Abdenry/sensorHubProject/CAD/FreeCAD/weatherStation/components/conduit/box/20241117_102958.jpg

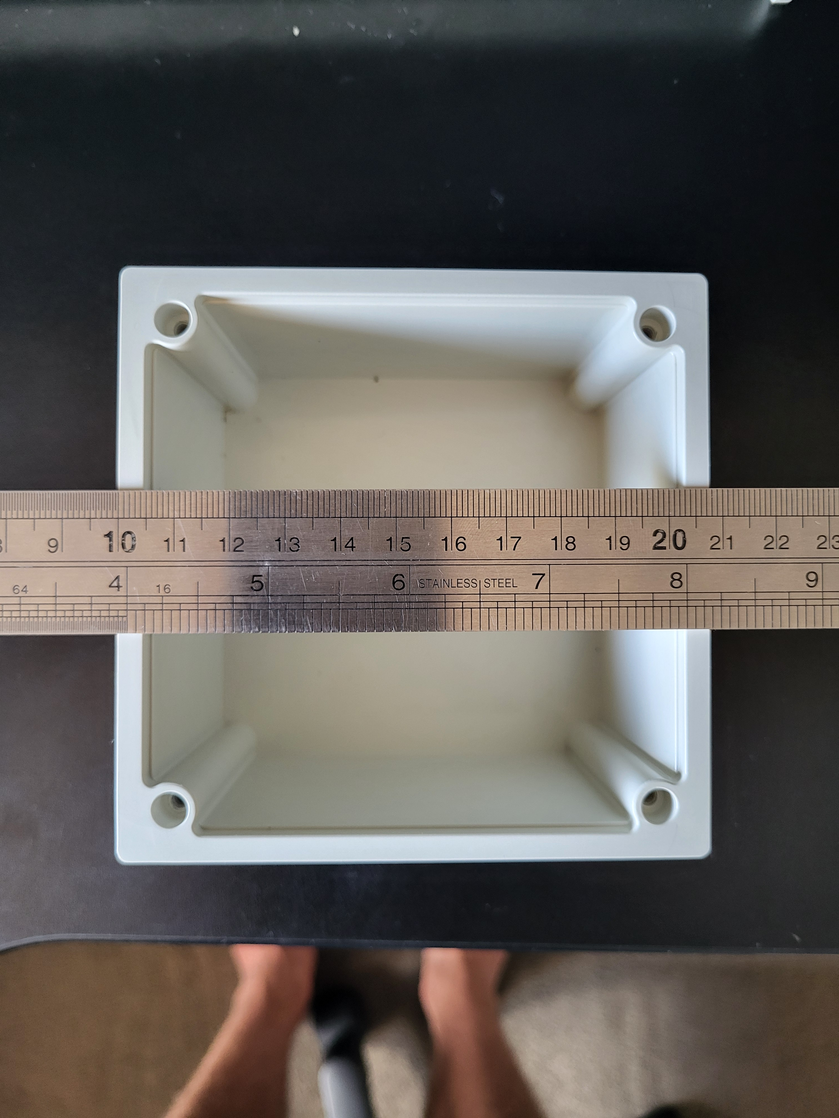
CAD/FreeCAD/weatherStation/components/conduit/box/20241117_102958.jpg
