Abdenry/sensorHubProject/CAD/FreeCAD/weatherStation/windVane/base/base.FCStd

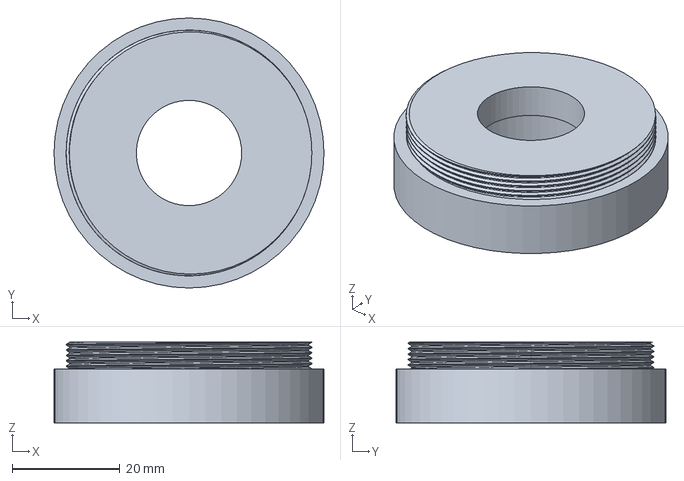
[picture p18: CAD file, 2025-01-13]
CAD/FreeCAD/weatherStation/windVane/base/base.FCStd
50.0 x 50.0 x 15.0 mm
