Abdenry/sensorHubProject/CAD/FreeCAD/weatherStation/windVane/middle/middle.FCStd

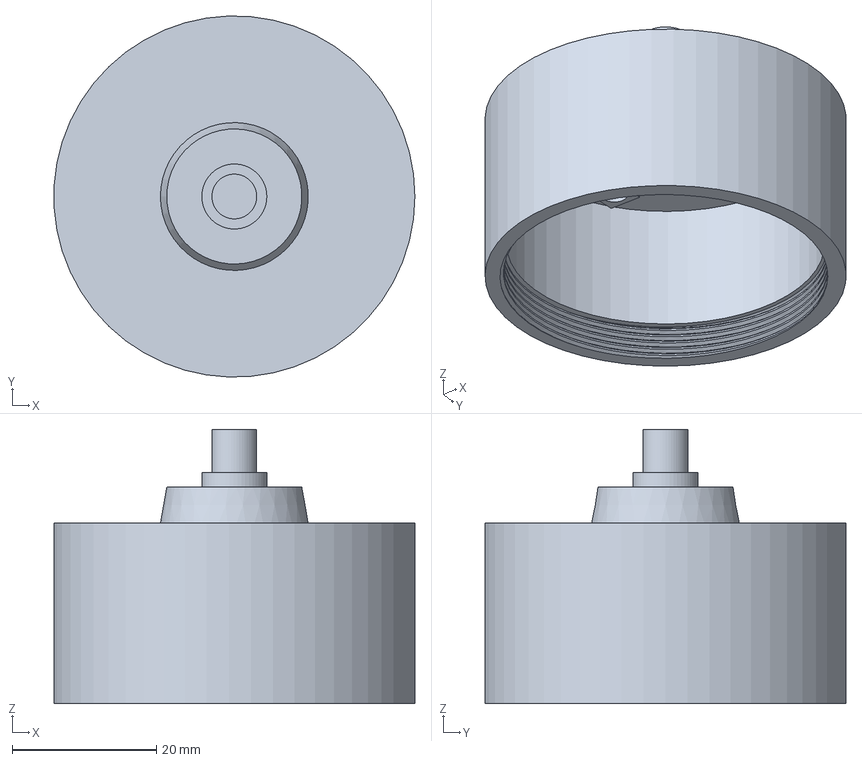
[picture p19: CAD file, 2025-01-13]
CAD/FreeCAD/weatherStation/windVane/middle/middle.FCStd
50.0 x 50.0 x 38.0 mm
