Abdenry/sensorHubProject/CAD/FreeCAD/weatherStation/windVane/top/top.FCStd

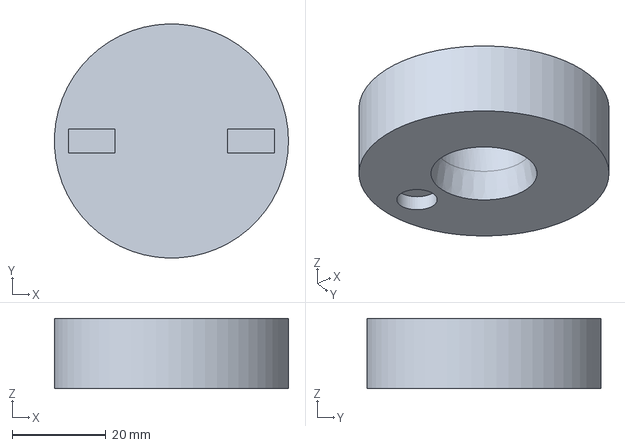
[picture p20: CAD file, 2025-03-11]
CAD/FreeCAD/weatherStation/windVane/top/top.FCStd
50.0 x 50.0 x 15.0 mm
