Abdenry/sensorHubProject/CAD/FreeCAD/weatherStation/windVane/vane/vane-Body.stl

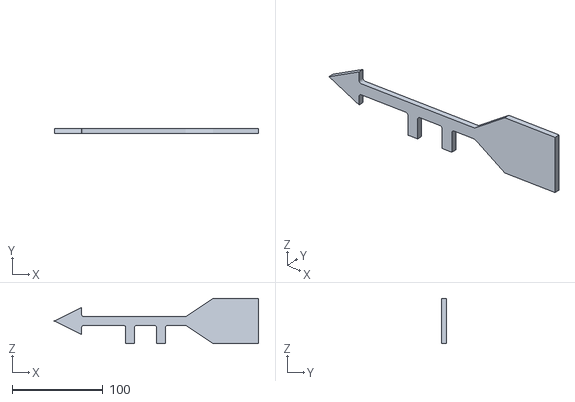
[picture p21: CAD file, 2025-02-10]
CAD/FreeCAD/weatherStation/windVane/vane/vane-Body.stl
225.0 x 5.00 x 50.0
