Abdenry/sensorHubProject/CAD/FreeCAD/weatherStation/anemometer/bearing/bearingTestFitOuter-Body.stl

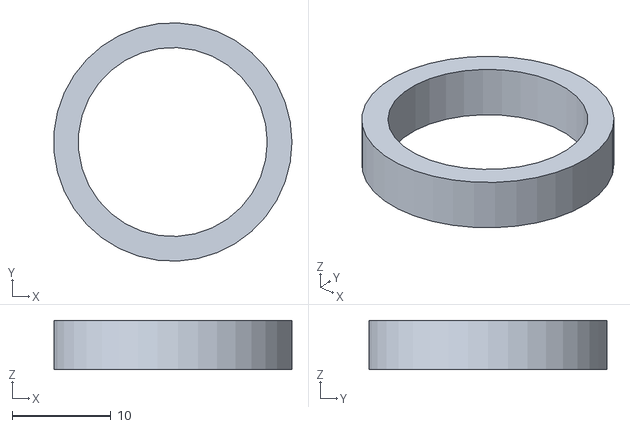
[picture p22: CAD file, 2024-11-20]
CAD/FreeCAD/weatherStation/anemometer/bearing/bearingTestFitOuter-Body.stl
24.1 x 24.1 x 5.00
