Abdenry/sensorHubProject/CAD/FreeCAD/weatherStation/anemometer/cover/cover-Cover.stl

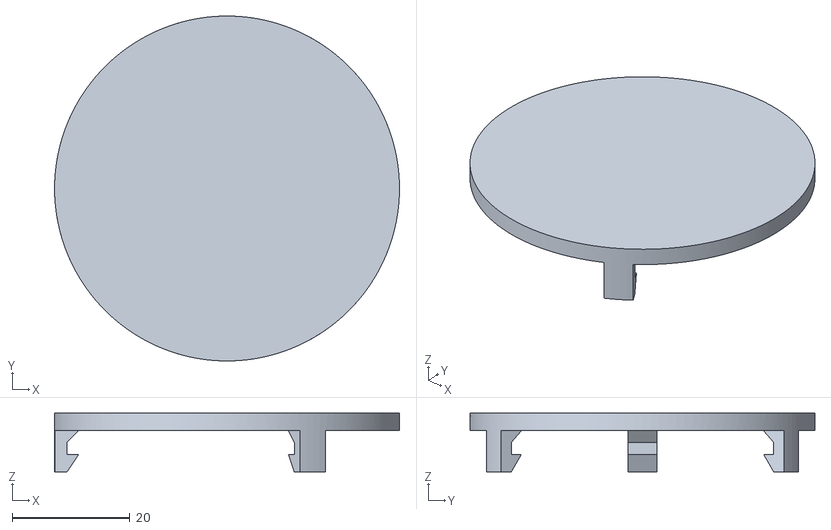
[picture p23: CAD file, 2025-02-10]
CAD/FreeCAD/weatherStation/anemometer/cover/cover-Cover.stl
58.5 x 58.5 x 10.0
