Abdenry/sensorHubProject/CAD/FreeCAD/weatherStation/components/conduit/box/lidWithGasket.FCStd

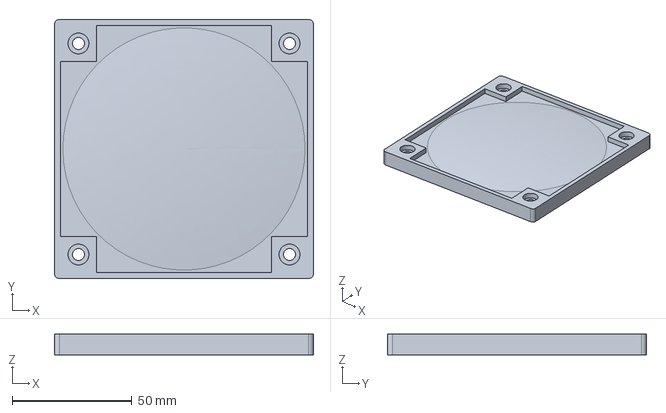
[picture p24: CAD file, 2024-11-20]
CAD/FreeCAD/weatherStation/components/conduit/box/lidWithGasket.FCStd
108.0 x 108.0 x 8.60 mm
