Abdenry/sensorHubProject/CAD/FreeCAD/weatherStation/components/conduit/straight100.FCStd

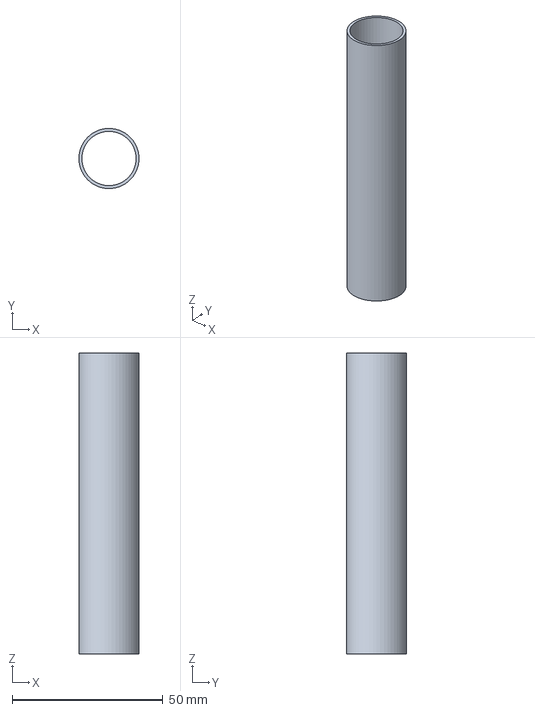
[picture p25: CAD file, 2025-01-13]
CAD/FreeCAD/weatherStation/components/conduit/straight100.FCStd
20.0 x 20.0 x 100.0 mm
