Abdenry/sensorHubProject/CAD/FreeCAD/weatherStation/conduitBase.FCStd

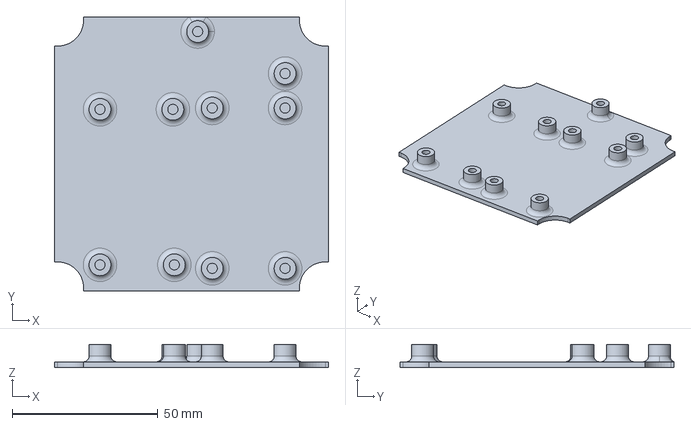
[picture p26: CAD file, 2025-01-13]
CAD/FreeCAD/weatherStation/conduitBase.FCStd
94.0 x 94.0 x 8.00 mm
