Abdenry/sensorHubProject/CAD/FreeCAD/weatherStation/powerSytem/5vStepDownStandoff.FCStd

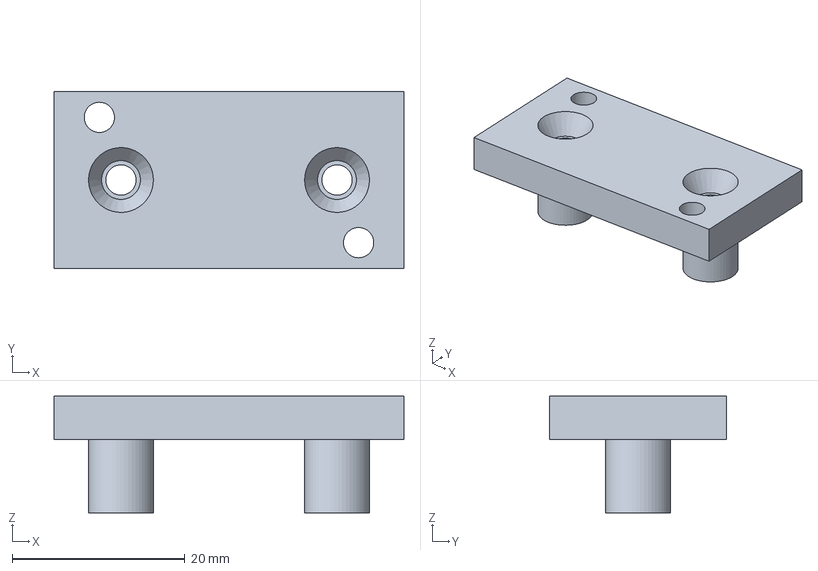
[picture p27: CAD file, 2025-02-10]
CAD/FreeCAD/weatherStation/powerSytem/5vStepDownStandoff.FCStd
40.5 x 20.5 x 13.5 mm
