Abdenry/sensorHubProject/CAD/FreeCAD/weatherStation/solarPanel/singlePieceFrame.FCStd

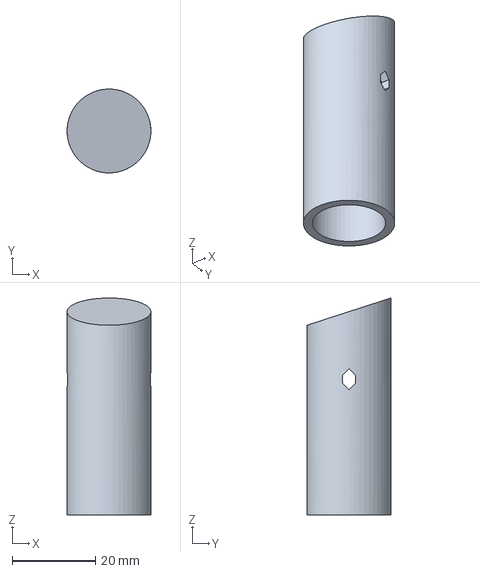
[picture p28: CAD file, 2025-03-06]
CAD/FreeCAD/weatherStation/solarPanel/singlePieceFrame.FCStd
20.1 x 20.1 x 52.0 mm
