Abdenry/sensorHubProject/CAD/FreeCAD/weatherStation/solarRadiationShield/middlePiece.FCStd

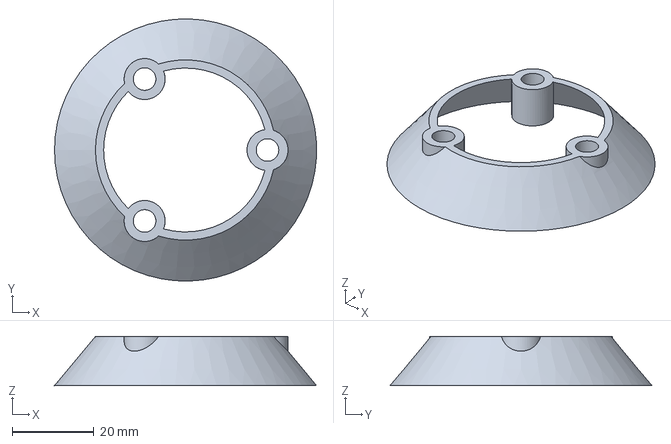
[picture p29: CAD file, 2025-02-10]
CAD/FreeCAD/weatherStation/solarRadiationShield/middlePiece.FCStd
64.0 x 64.0 x 12.0 mm
