Abdenry/sensorHubProject/CAD/FreeCAD/weatherStation/anemometer/bearing/bearingTestFitInner.FCStd

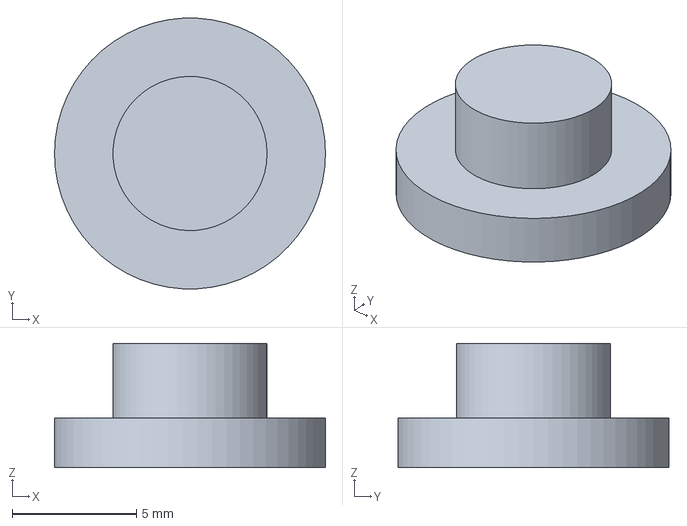
[picture p30: CAD file, 2024-11-20]
CAD/FreeCAD/weatherStation/anemometer/bearing/bearingTestFitInner.FCStd
10.9 x 10.9 x 5.00 mm
