Abdenry/sensorHubProject/CAD/FreeCAD/weatherStation/anemometer/cover/cover-Body.stl

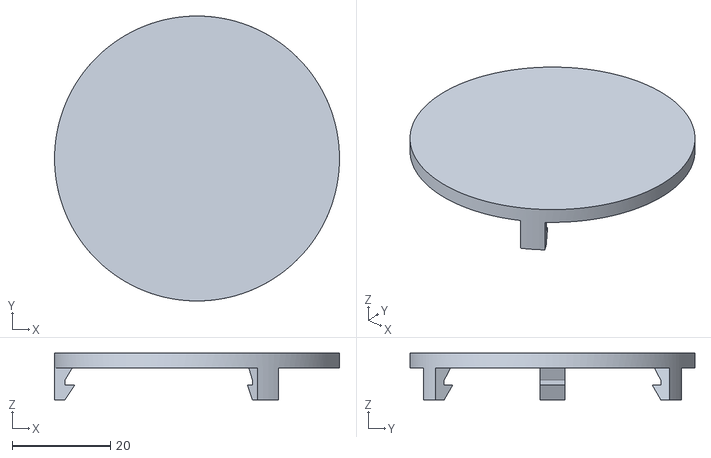
[picture p31: CAD file, 2024-12-03]
CAD/FreeCAD/weatherStation/anemometer/cover/cover-Body.stl
58.0 x 58.0 x 9.50
