Abdenry/sensorHubProject/CAD/FreeCAD/weatherStation/components/conduit/coupling.FCStd

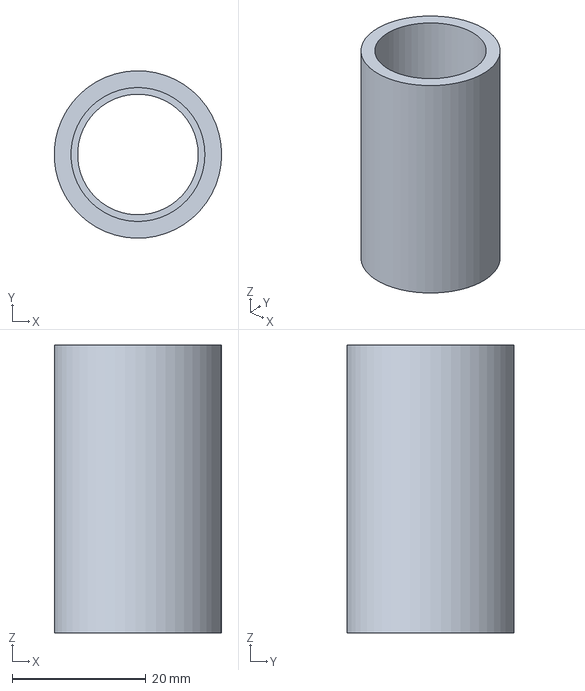
[picture p32: CAD file, 2025-01-13]
CAD/FreeCAD/weatherStation/components/conduit/coupling.FCStd
25.0 x 25.0 x 43.0 mm
