Abdenry/sensorHubProject/CAD/FreeCAD/weatherStation/powerSytem/StepDownStandoff-Body.stl

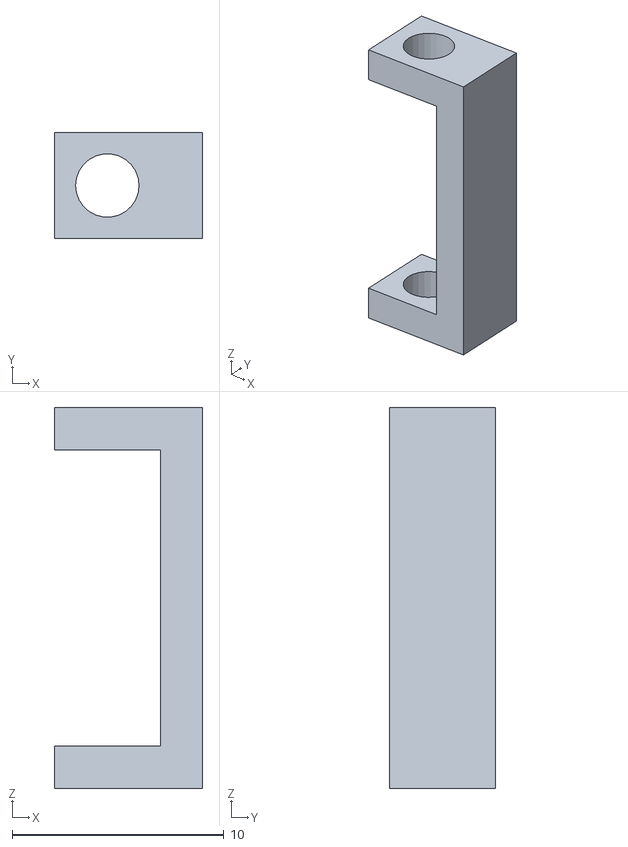
[picture p33: CAD file, 2025-02-10]
CAD/FreeCAD/weatherStation/powerSytem/StepDownStandoff-Body.stl
7.00 x 5.00 x 18.0
