Abdenry/sensorHubProject/CAD/FreeCAD/weatherStation/components/conduit/adapter.FCStd

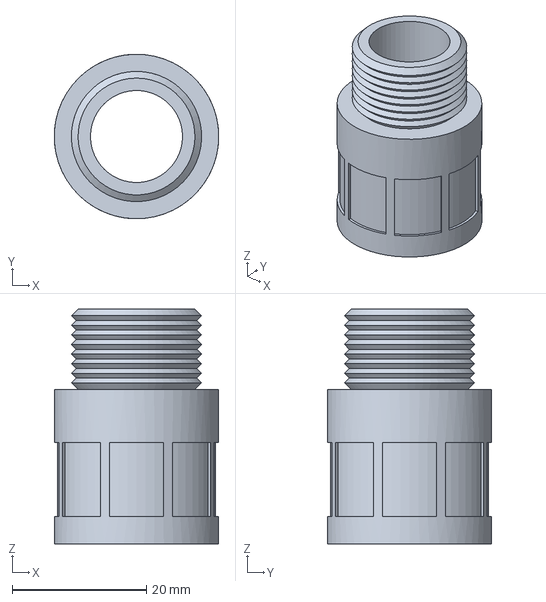
[picture p34: CAD file, 2025-01-13]
CAD/FreeCAD/weatherStation/components/conduit/adapter.FCStd
24.5 x 24.5 x 35.0 mm
