Abdenry/sensorHubProject/CAD/FreeCAD/weatherStation/powerSytem/5vStepDownStandoff2-Body.stl

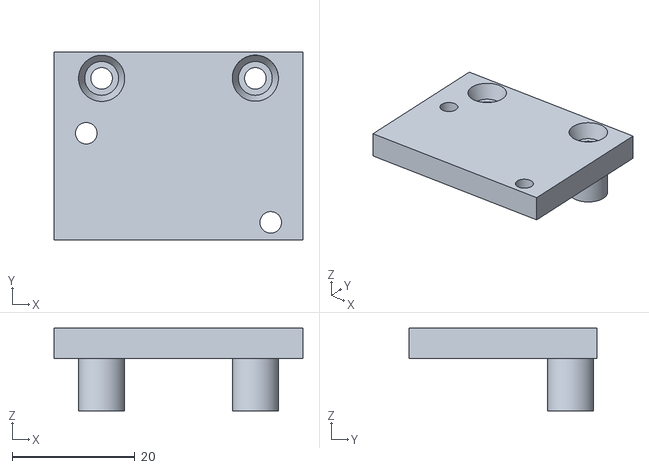
[picture p35: CAD file, 2025-02-10]
CAD/FreeCAD/weatherStation/powerSytem/5vStepDownStandoff2-Body.stl
40.5 x 30.5 x 13.5
