Abdenry/sensorHubProject/CAD/FreeCAD/weatherStation/powerSytem/5vStepDownStandoff-Body.stl

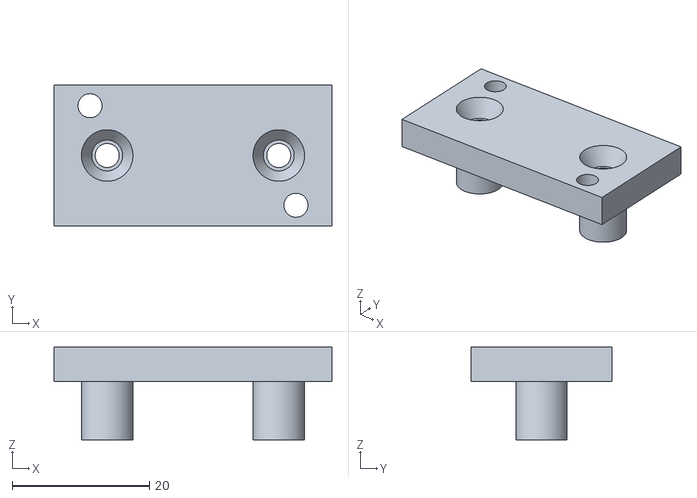
[picture p36: CAD file, 2025-02-10]
CAD/FreeCAD/weatherStation/powerSytem/5vStepDownStandoff-Body.stl
40.5 x 20.5 x 13.5
