Abdenry/sensorHubProject/CAD/FreeCAD/weatherStation/solarPanel/couplingNut.FCStd

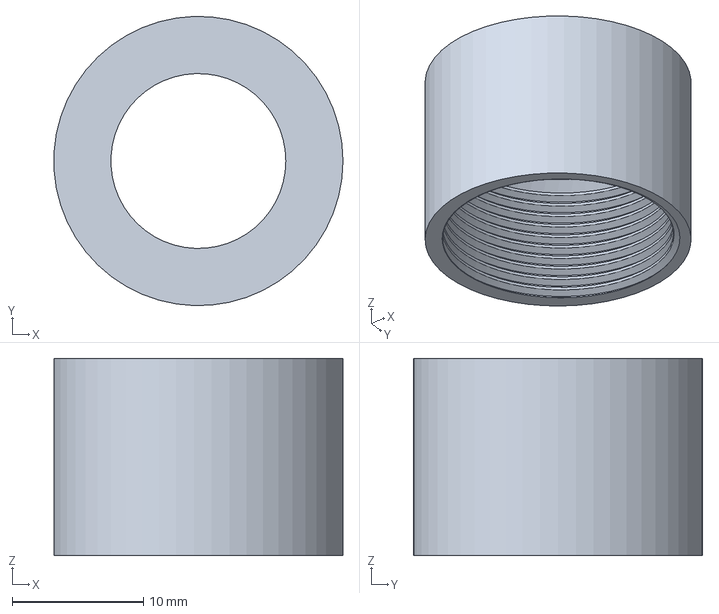
[picture p37: CAD file, 2025-01-13]
CAD/FreeCAD/weatherStation/solarPanel/couplingNut.FCStd
22.0 x 22.0 x 15.0 mm
