Abdenry/sensorHubProject/CAD/FreeCAD/weatherStation/solarRadiationShield/base.FCStd

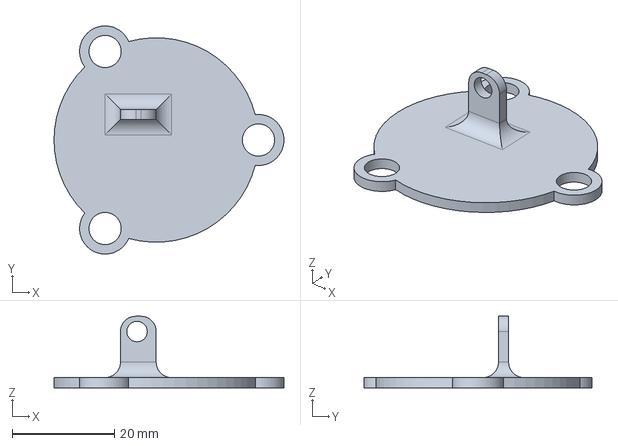
[picture p38: CAD file, 2025-02-10]
CAD/FreeCAD/weatherStation/solarRadiationShield/base.FCStd
45.0 x 44.6 x 14.0 mm
