Abdenry/sensorHubProject/CAD/FreeCAD/weatherStation/components/conduit/tShape.FCStd

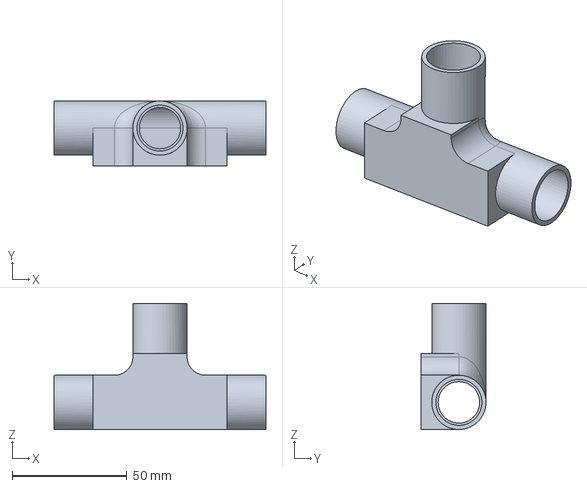
[picture p39: CAD file, 2025-01-13]
CAD/FreeCAD/weatherStation/components/conduit/tShape.FCStd
92.2 x 28.3 x 54.8 mm
