Abdenry/sensorHubProject/CAD/FreeCAD/weatherStation/solarPanel/solarBed.stl

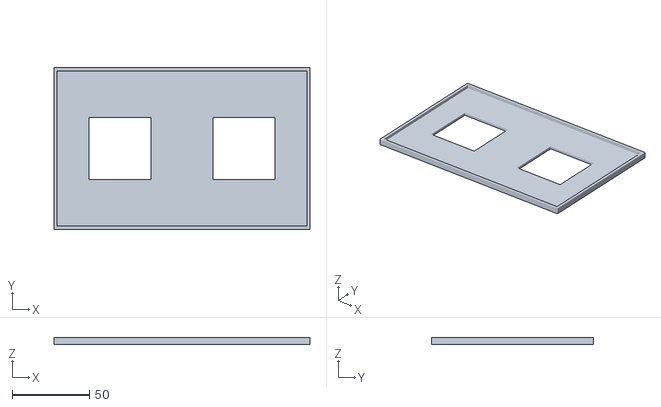
[picture p40: CAD file, 2025-01-13]
CAD/FreeCAD/weatherStation/solarPanel/solarBed.stl
165.4 x 104.4 x 4.50
