Abdenry/sensorHubProject/CAD/FreeCAD/weatherStation/components/conduit/adapterRing.FCStd

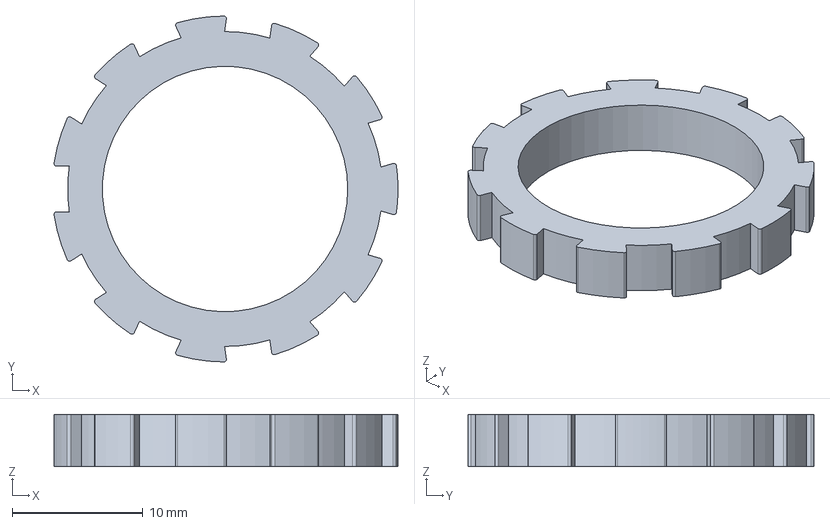
[picture p41: CAD file, 2025-01-13]
CAD/FreeCAD/weatherStation/components/conduit/adapterRing.FCStd
26.4 x 26.5 x 4.00 mm
