Abdenry/sensorHubProject/CAD/FreeCAD/weatherStation/powerSytem/pcbPowerBoardSize.FCStd

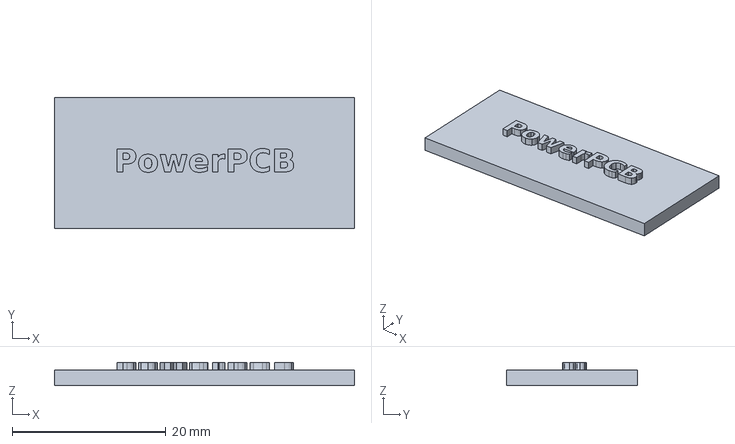
[picture p42: CAD file, 2024-12-05]
CAD/FreeCAD/weatherStation/powerSytem/pcbPowerBoardSize.FCStd
39.0 x 17.0 x 3.00 mm
