Abdenry/sensorHubProject/CAD/FreeCAD/weatherStation/components/conduit/straight300.FCStd

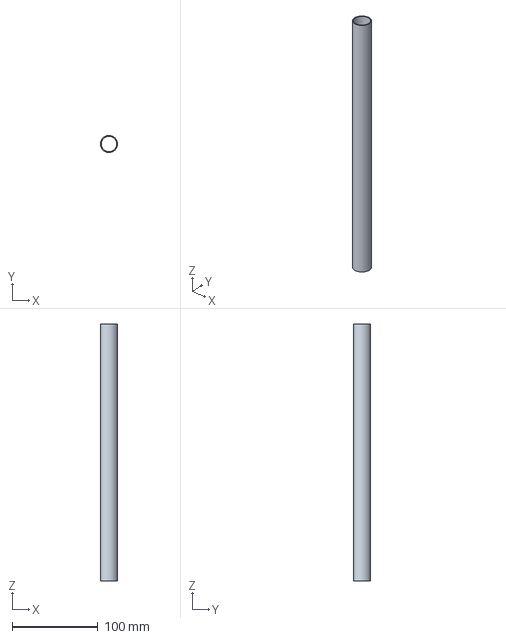
[picture p43: CAD file, 2024-11-20]
CAD/FreeCAD/weatherStation/components/conduit/straight300.FCStd
20.0 x 20.0 x 300.0 mm
