Abdenry/sensorHubProject/CAD/FreeCAD/weatherStation/solarPanel/secondStraightPipe.FCStd

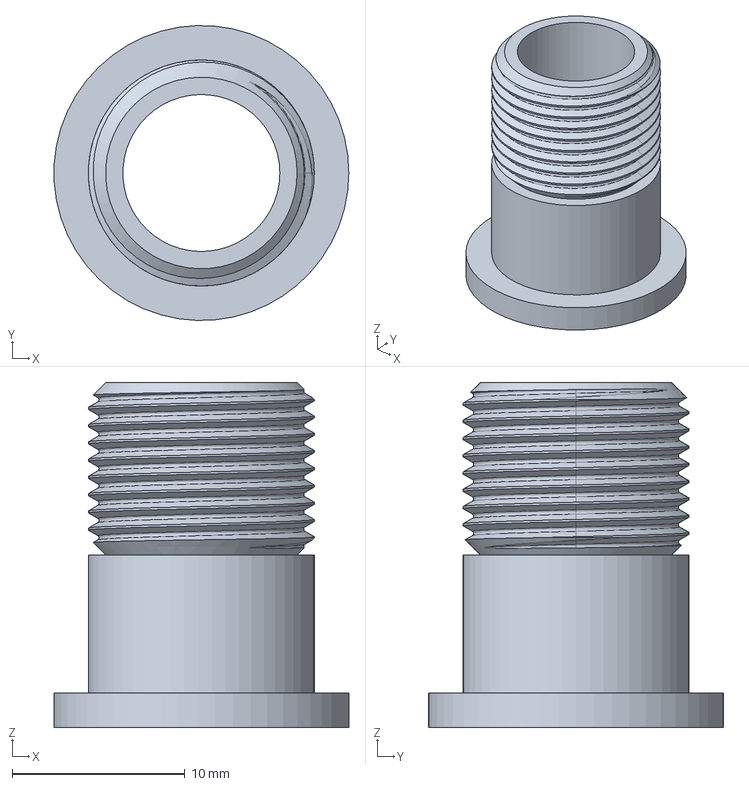
[picture p44: CAD file, 2025-01-13]
CAD/FreeCAD/weatherStation/solarPanel/secondStraightPipe.FCStd
17.1 x 17.1 x 20.0 mm
