Abdenry/sensorHubProject/CAD/FreeCAD/weatherStation/components/conduit/90Degree.FCStd

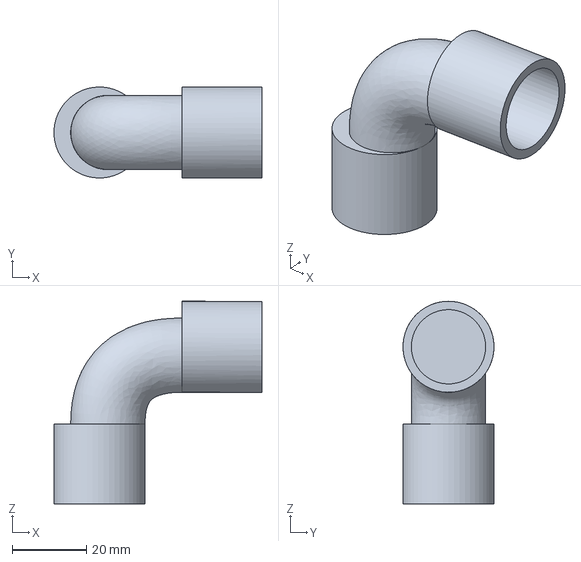
[picture p45: CAD file, 2024-11-20]
CAD/FreeCAD/weatherStation/components/conduit/90Degree.FCStd
56.0 x 24.5 x 54.5 mm
