Abdenry/sensorHubProject/CAD/FreeCAD/weatherStation/solarPanel/firstStraightPipe.FCStd

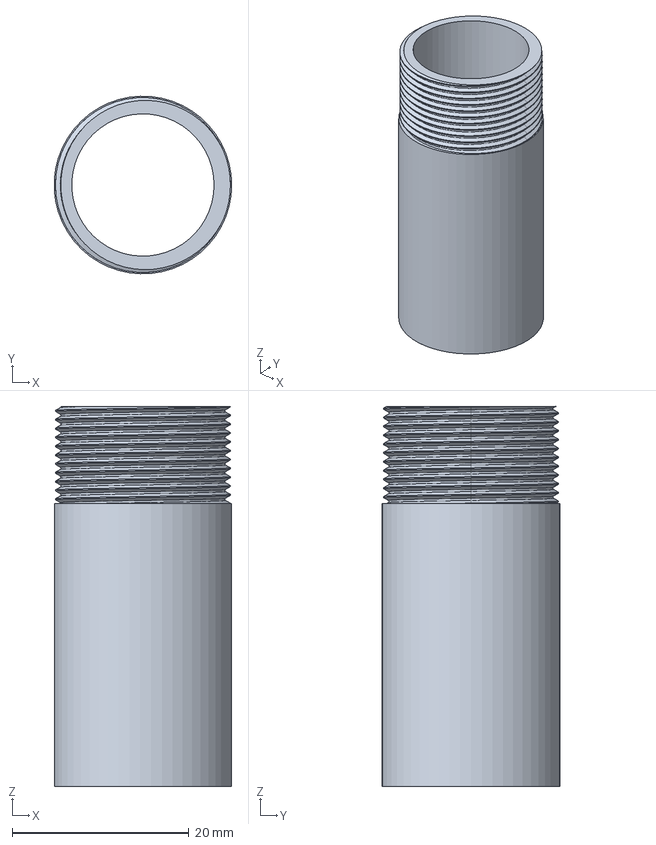
[picture p46: CAD file, 2025-01-13]
CAD/FreeCAD/weatherStation/solarPanel/firstStraightPipe.FCStd
20.1 x 20.1 x 43.0 mm
