Abdenry/sensorHubProject/CAD/FreeCAD/weatherStation/solarPanel/solarFrame.FCStd

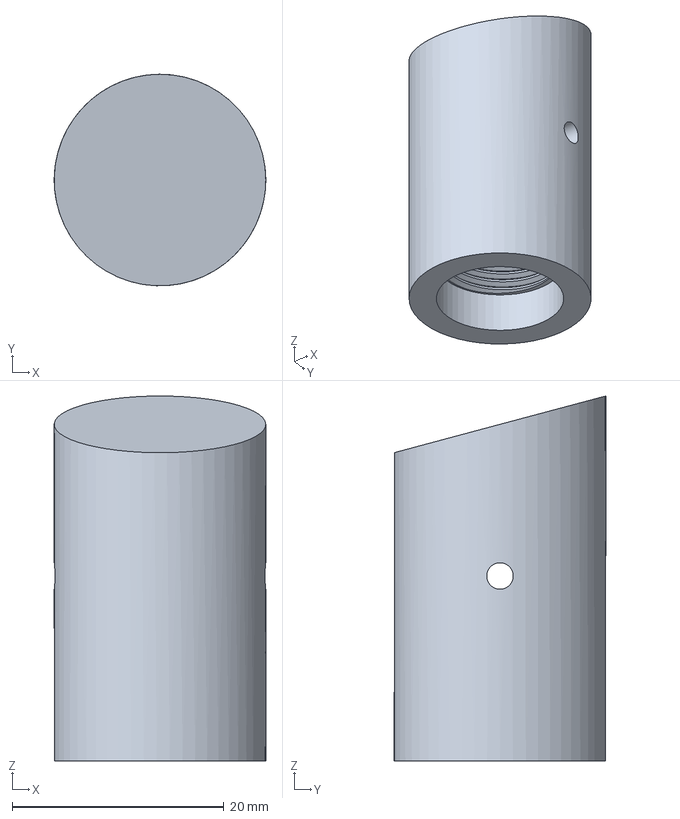
[picture p47: CAD file, 2025-01-13]
CAD/FreeCAD/weatherStation/solarPanel/solarFrame.FCStd
20.0 x 20.0 x 34.5 mm
